f1rmb/aDCLoad/eagle/aDCLoad/Main.png

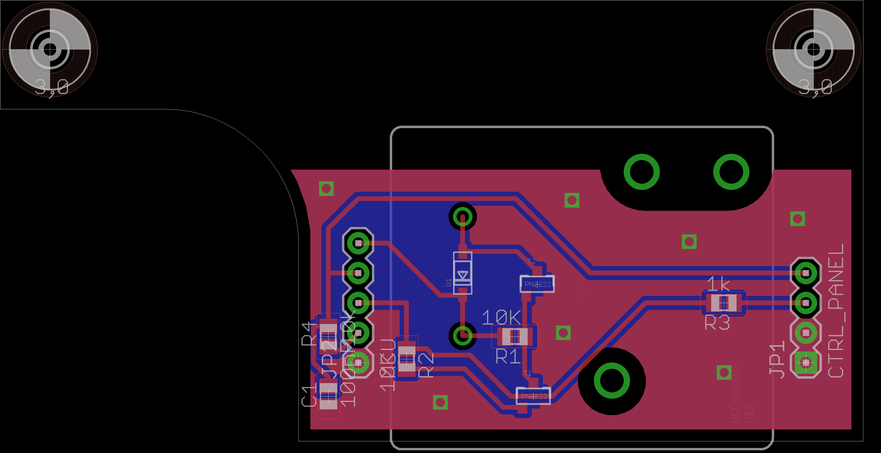
eagle/aDCLoad/Main.png
