f1rmb/aDCLoad/eagle/aDCLoad/PCB_BOTTOM.png

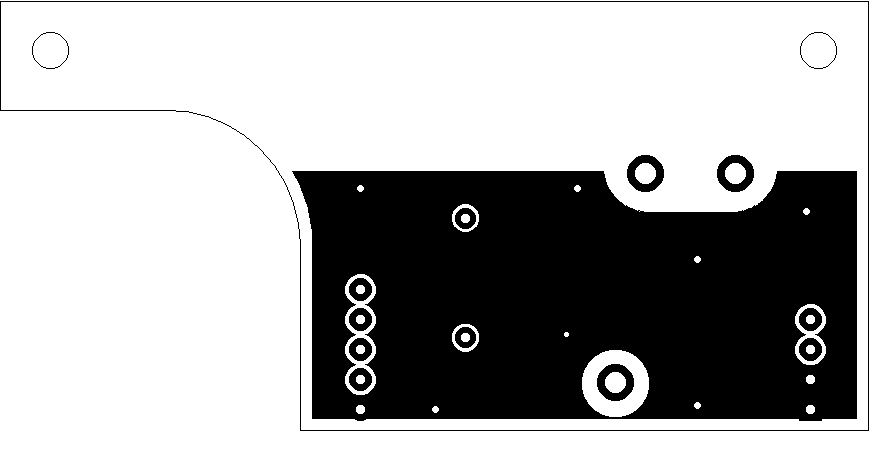
eagle/aDCLoad/PCB_BOTTOM.png
