f1rmb/aDCLoad/eagle/aDCLoad/PCB_TOP.png

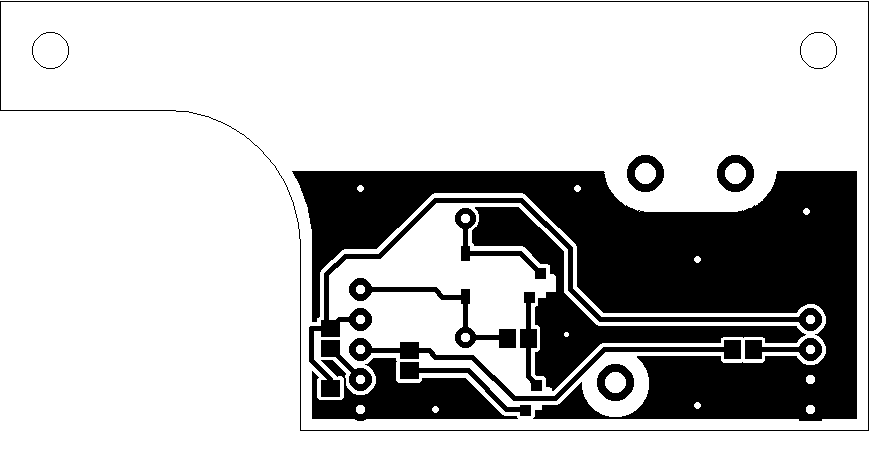
eagle/aDCLoad/PCB_TOP.png
